kazik-code/boost-converter/simulation/BOOST_END.asc

C1: cap; 200µ
C2: cap; 2.2µ
C4: cap; 200p
D1: diode; 1N5819
I1: current; PULSE(0 0.8 20m 1u 1u 5m 1)
L1: ind; 40µ; Rser=1m
M1: pmos; IRF9640
Q1: pnp; BC557B
R1: res; 83k
R2: res; 12k
R3: res; 40
R4: res; 51k
R5: res; 1.3
R6: res; 3k
R7: res; 33k
R8: res; 10k
U1: LT1930
V1: voltage; 4
Named nets: 0
.tran 50m
